andykarpov/karabas-megabuzz/docs/karabas-megabuzz_revA1_bottom.png

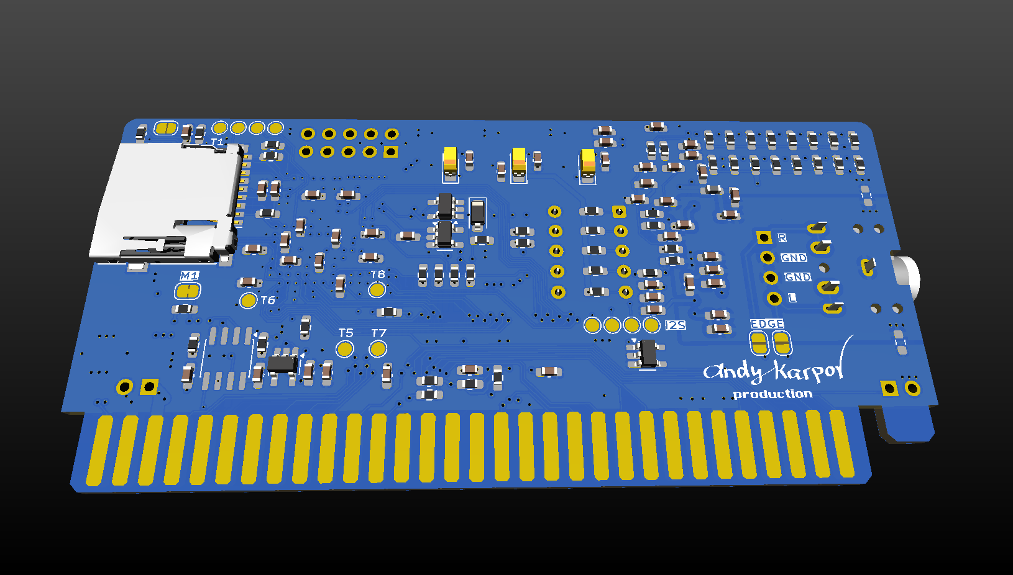
docs/karabas-megabuzz_revA1_bottom.png
