andykarpov/karabas-megabuzz/docs/karabas-megabuzz_revA2_top_map.png

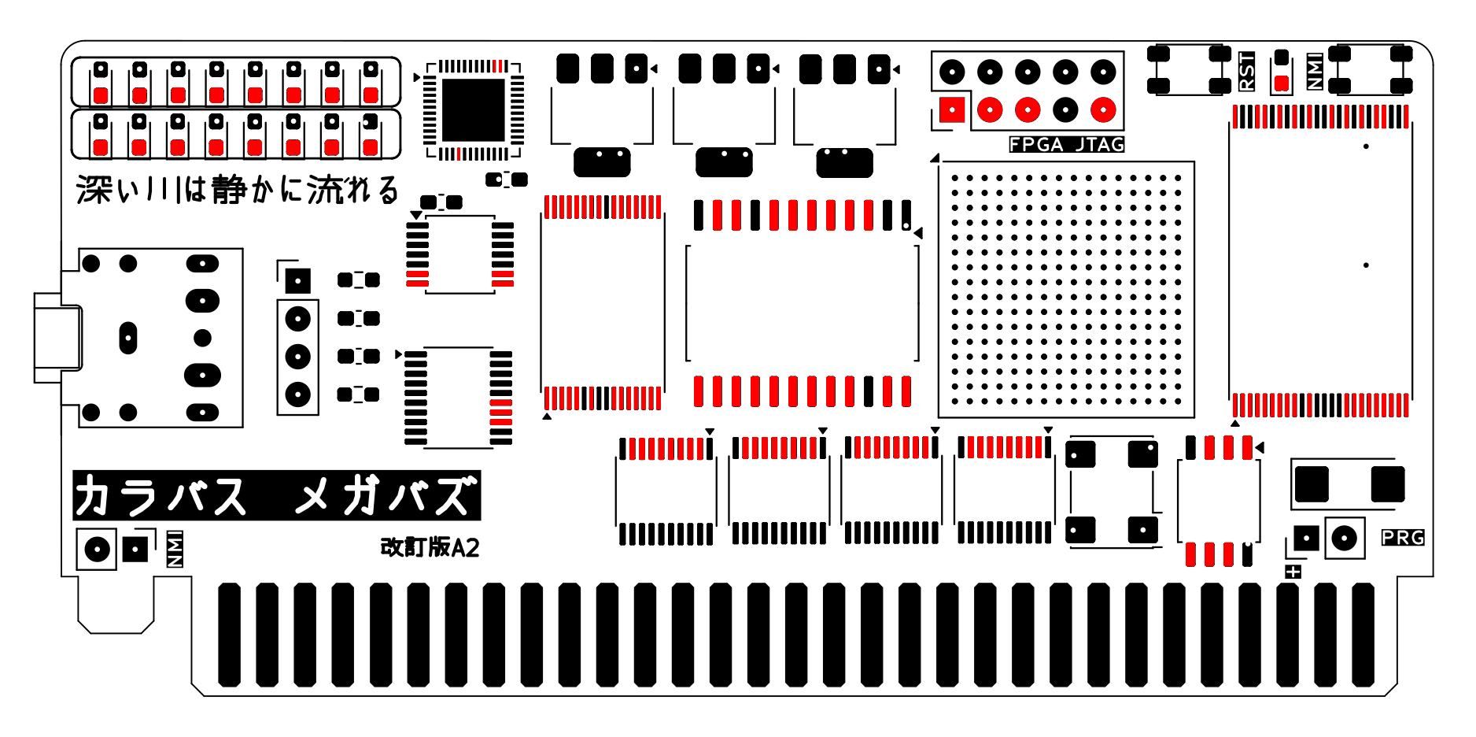
docs/karabas-megabuzz_revA2_top_map.png
