andykarpov/karabas-megabuzz/docs/karabas-megabuzz_revA_top_map.png

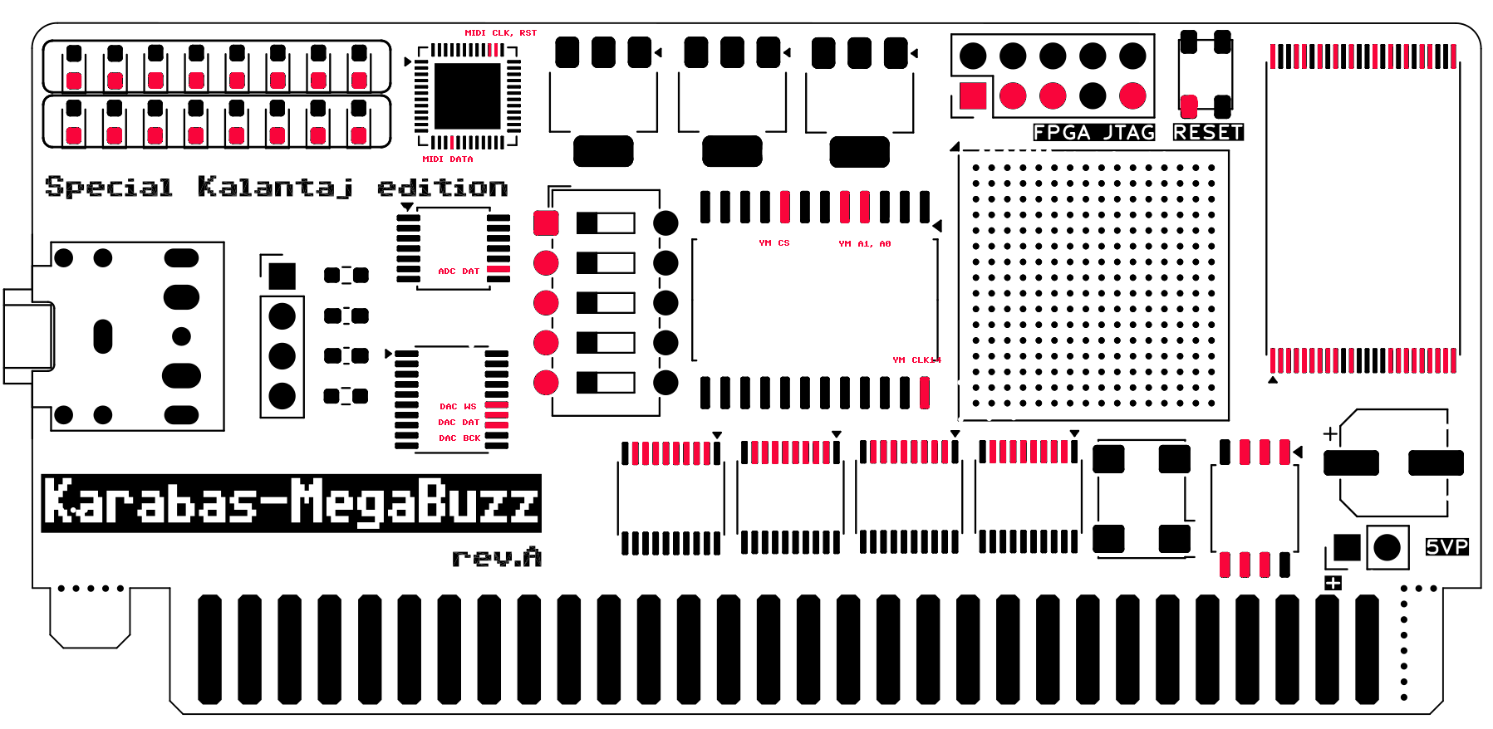
docs/karabas-megabuzz_revA_top_map.png
