andykarpov/karabas-megabuzz/firmware/src/rtl/top_a2.v

/*-------------------------------------------------------------------------------------------------------------------
-- 
-- 
-- #       #######                                                 #                                               
-- #                                                               #                                               
-- #                                                               #                                               
-- ############### ############### ############### ############### ############### ############### ############### 
-- #             #               # #                             # #             #               # #               
-- #             # ############### #               ############### #             # ############### ############### 
-- #             # #             # #               #             # #             # #             #               # 
-- #             # ############### #               ############### ############### ############### ############### 
--                                                                                                                 
--         ####### ####### ####### #######          ## ##   ######  #####   #####  ######  #     # ####### #######
--                                                 #  #  # #       #       #     # #     # #     #      ##      ##
--                                                 #  #  # #####   #   ### ####### ######  #     #   ###     ### 
--                                                 #  #  # #       #     # #     # #     # #     # ##      ##     
--                                                 #  #  #  ######  #####  #     # ######   #####  ####### #######
--
-- https://github.com/andykarpov/karabas-megabuzz
-- FPGA firmware for Karabas-MegaBuzz soundcard revA2
--
-- @author Andy Karpov <andy.karpov@gmail.com>
-- EU, 2026
------------------------------------------------------------------------------------------------------------------*/
`default_nettype none

module karabas_megabuzz_a2(
    input wire          clk,
    input wire  [5:5]   cfg_n,
    input wire          btn_reset_n,
    input wire          btn_nmi_n,

    output wire         o_reset_n,
    input wire          bus_rst_n,
    input wire  [15:0]  bus_a,
    inout wire  [7:0]   bus_d,
    input wire          bus_rd_n,
    input wire          bus_wr_n,
    input wire          bus_iorq_n,
    input wire          bus_mreq_n,
    input wire          bus_m1_n,
    output wire         bus_wait_n,
    output wire         bus_iorqge_n,
    inout wire          bus_nmi_n,
    output wire         bus_romcs_n,
    input wire          bus_f14,

    output wire         midi_clk,
    output wire         midi_tx,
    output wire         midi_reset_n,

    output wire [20:0]  mem_a,
    inout wire  [7:0]   mem_d,
    output wire         mem_wr_n,
    output wire         mem_rd_n,

    output wire [16:13] mmc_mem_a,
    output wire         mmc_mem_cs_n,
    output wire         mmc_mem_rd_n,
    output wire         mmc_mem_wr_n,

    inout wire          sda,
    inout wire          scl,

    output wire         opl3_clk,
    output wire [1:0]   opl3_a,
    output wire         opl3_cs_n,
    input wire  [1:0]   opl3_smp,
    input wire          opl3_data,
    input wire          opl3_dclk,

    output wire         adc_clk,
    output wire         adc_bck,
    output wire         adc_lrck,
    input wire          adc_dat,

    output wire         dac_bck,
    output wire         dac_ws,
    output wire         dac_dat,

    output wire         flash_cs_n,
    output wire         flash_sck,
    inout wire          flash_mosi,
    inout wire          flash_miso,
    inout wire          flash_hold_n,
    inout wire          flash_wp_n,
    output wire         psram_cs_n,

    output wire         sd_cs_n,
    output wire         sd_clk,
    inout wire          sd_di,
    inout wire          sd_do,
    input wire          sd_det_n,

    output wire [7:0]   led_meter_l,
    output wire [7:0]   led_meter_r,

    output wire         led1,

    inout wire  [4:1]   tp
);

// unused signals
assign flash_hold_n = 1'b1;
assign flash_wp_n   = 1'b1;
assign psram_cs_n   = 1'b1;
assign tp[4:1]      = 4'bz;
assign led1         = sd_cs_n;
assign sda          = 1'bz;
assign scl          = 1'b1;

// config bits expanded to named signals
wire [7:0] cfg_byte; // todo: fetch cfg from flash (default) + eeprom
wire divmmc_en      = cfg_byte[0];
wire zc_en          = cfg_byte[1];
wire soundrive_en   = cfg_byte[2];
wire beeper_en      = cfg_byte[3];
wire saa_en         = cfg_byte[4];
wire gs_en          = cfg_byte[5];
wire turbosound_en  = cfg_byte[6];
wire midi_en        = cfg_byte[6]; // depends on AY port
wire opl3_en        = cfg_byte[7];

wire vu_reverse     = ~cfg_n[5]; // solder jumper (reversed VU meters)

// pll
wire clk_bus, clk_mem, clk12, locked, areset;
pll pll_inst(
    .CLK_IN1         (clk),
    .CLK_OUT1        (clk_mem), // 140
    .CLK_OUT2        (clk_bus), // 28
    .CLK_OUT3        (clk12),   // 12
    .LOCKED          (locked)
);
assign areset = ~locked;

// poweron reset
wire poweron_reset;
resetter poweron_resetter(.clk(clk_bus), .areset(divmmc_en & loader_reset), .reset_in(divmmc_en & loader_reset), .reset_out(poweron_reset));

assign o_reset_n = (poweron_reset) ? 1'b0 : 1'bz;

// clock for gs and opl3
reg ce_14m;
always @(negedge clk_bus)
    ce_14m <= !ce_14m;

// reset
wire reset;
wire reset_short;
resetter resetter(.clk(clk_bus), .areset(areset), .reset_in(~bus_rst_n || ~btn_reset_n || poweron_reset), .reset_out(reset), .reset_short(reset_short));

assign midi_reset_n = ~reset;

// bus_iorq_n is useless on zxevo :(
// so we're detecting bus_iorq_n cycle by bus_rd_n/bus_wr_n signal asserted without bus_m1_n/bus_mreq_n
reg ioreq, ioreq_prev;
always @(negedge clk_mem) begin
    ioreq_prev  <= ioreq;
    ioreq       <= bus_m1_n && bus_mreq_n && (~bus_rd_n || ~bus_wr_n);
end
wire ioreq_rd = ioreq && ~bus_rd_n;
wire ioreq_wr = ioreq && ~bus_wr_n;

// bus_dos_n is useless on zxevo :(
// so we're just lock some ports access when instruction has been fetched from rom
reg rom_m1_access;
always @(negedge clk_mem or posedge reset) begin
    if (reset)
        rom_m1_access <= 0;
    else if (~bus_m1_n)
        rom_m1_access <= bus_a[15:14] == 2'b00;
end

// ------- flash ----------------
wire [23:0] flash_a_bus;
wire [7:0] flash_do_bus;
wire flash_wr_n, flash_rd_n, flash_er_n, flash_busy, flash_rdy;
flash flash(
    .CLK              (clk_bus),
    .RESET            (areset),

    .A                (flash_a_bus),
    .DI               (8'hFF),
    .DO               (flash_do_bus),
    .WR_N             (1'b1),
    .RD_N             (flash_rd_n),
    .ER_N             (1'b1),
    
    .DATA0            (flash_miso),
    .NCSO             (flash_cs_n),
    .DCLK             (flash_sck),
    .ASDO             (flash_mosi),

    .BUSY             (flash_busy),
    .DATA_READY       (flash_rdy)
);

// -------- loader --------------
wire [20:0] loader_ram_a;
wire [7:0] loader_ram_do;
wire loader_act, loader_reset, loader_ram_wr;
loader loader(
    .CLK              (clk_bus),
    .RESET            (areset),
    
    .RAM_A            (loader_ram_a),
    .RAM_DO           (loader_ram_do),
    .RAM_WR           (loader_ram_wr),

    .CFG              (cfg_byte),

    .FLASH_A          (flash_a_bus),
    .FLASH_DO         (flash_do_bus),
    .FLASH_RD_N       (flash_rd_n),
    .FLASH_BUSY       (flash_busy),
    .FLASH_READY      (flash_rdy),
    
    .LOADER_ACTIVE    (loader_act),
    .LOADER_RESET     (loader_reset)
);

// ------- i2s DAC --------------
wire signed [15:0] audio_mix_l, audio_mix_r;

PCM5102 #(.DAC_CLK_DIV_BITS(2)) dac_inst(
    .clk              (clk_bus),
    .reset            (reset),
    .left             (audio_mix_l),
    .right            (audio_mix_r),
    .din              (dac_dat),
    .bck              (dac_bck),
    .lrck             (dac_ws)
);

// ------- PCM1808 ADC ---------
wire signed [23:0] adc_l, adc_r;

i2s_transceiver adc_inst(
    .reset_n          (~reset),
    .mclk             (clk_bus),
    .sclk             (adc_bck),
    .ws               (adc_lrck),
    .sd_tx            (),
    .sd_rx            (adc_dat),
    .l_data_tx        (24'b0),
    .r_data_tx        (24'b0),
    .l_data_rx        (adc_l),
    .r_data_rx        (adc_r)
);

ODDR2 oddr_adc2(.Q(adc_clk), .C0(clk_bus), .C1(~clk_bus), .CE(1'b1), .D0(1'b1), .D1(1'b0), .R(1'b0), .S(1'b0));
ODDR2 oddr_midi(.Q(midi_clk), .C0(clk12), .C1(~clk12), .CE(1'b1), .D0(1'b1), .D1(1'b0), .R(1'b0), .S(1'b0));

// ------- SOUNDRIVE ----------
wire [7:0] covox_a, covox_b, covox_c, covox_d, covox_fb;

soundrive soundrive_inst(
    .clk              (clk_bus),
    .reset            (reset),
    .cs               (soundrive_en),
    .a                (bus_a),
    .d                (bus_d),
    .ioreq_wr         (ioreq_wr),
    .rom_m1_access    (rom_m1_access),
    .out_a            (covox_a),
    .out_b            (covox_b),
    .out_c            (covox_c),
    .out_d            (covox_d),
    .out_fb           (covox_fb)
);

// ------- BEEPER --------------
wire beeper;
beeper beeper_inst(
    .clk              (clk_bus),
    .reset            (reset),
    .cs               (beeper_en),
    .a                (bus_a),
    .d                (bus_d),
    .ioreq_wr         (ioreq_wr),
    .out_beeper       (beeper)
);

// SAA1099

wire [7:0] saa_out_l, saa_out_r;
wire saa_wr_n = ~(ioreq_wr && bus_a[7:0] == 8'hFF && ~rom_m1_access);

wire ce_8;
clk_div_8mhz saa1099_cen_inst(
    .clk              (clk_bus),
    .rst_n            (~areset),
    .cen              (ce_8)
);

saa1099 saa1099_inst(
    .clk_sys          (clk_bus),
     .ce              (ce_8),
    .rst_n            (~reset),
    .cs_n             (~saa_en),
    .a0               (bus_a[8]),
    .wr_n             (saa_wr_n),
    .din              (bus_d),
    .out_l            (saa_out_l),
    .out_r            (saa_out_r)
);

// turbosound fm
wire ts_enable = turbosound_en & ioreq & bus_a[15] & (bus_a[3:0] == 4'b1101);
wire ts_we     = ts_enable & ioreq_wr;
wire [7:0] ts_do;
wire [7:0] ts_ssg0_a, ts_ssg0_b, ts_ssg0_c, ts_ssg1_a, ts_ssg1_b, ts_ssg1_c;
wire [15:0] ts_ssg0_fm, ts_ssg1_fm;
wire ts_fm_ena;

reg ce_ym;
reg [2:0] div;
always @(posedge clk_bus) begin
    div <= div + 1'd1;
    ce_ym <= !div[2] & !div[1] & !div[0]; // 3.5
end

turbosound turbosound_inst(
    .CLK              (clk_bus),
    .RESET            (reset),
    .CE               (ce_ym),
    .BDIR             (ts_we),
    .BC               (bus_a[14]),
    .DI               (bus_d),
    .DO               (ts_do),
    .AY_MODE          (1'b0), // ay / ym
        
    .SSG0_AUDIO_A     (ts_ssg0_a),
    .SSG0_AUDIO_B     (ts_ssg0_b),
    .SSG0_AUDIO_C     (ts_ssg0_c),

    .SSG1_AUDIO_A     (ts_ssg1_a),
    .SSG1_AUDIO_B     (ts_ssg1_b),
    .SSG1_AUDIO_C     (ts_ssg1_c),
    
    .SSG0_AUDIO_FM    (ts_ssg0_fm),
    .SSG1_AUDIO_FM    (ts_ssg1_fm),
    
    .SSG_FM_ENA       (ts_fm_ena),
    .MIDI_TX          (midi_tx)
);

// ------- GS

wire gs_oe;
wire [7:0] gs_do_bus;
wire [14:0] gs_out_l, gs_out_r;

gs_top gs_inst(
    .clk_bus          (clk_bus),
     .ce              (ce_14m),
    .reset            (reset),

    .a                (bus_a),
    .di               (bus_d),
    .mreq_n           (bus_mreq_n),
    .iorq_n           (bus_iorq_n),
    .m1_n             (bus_m1_n),
    .rd_n             (bus_rd_n),
    .wr_n             (bus_wr_n),

    .oe               (gs_oe),
    .do_bus           (gs_do_bus),

    .sram_d           (mem_d),
    .sram_a           (mem_a),
    .sram_wr_n        (mem_wr_n),
    .sram_rd_n        (mem_rd_n),
     
    .loader_act       (loader_act),
    .loader_ram_a     (loader_ram_a),
    .loader_ram_do    (loader_ram_do),
    .loader_ram_wr    (loader_ram_wr),

    .out_l            (gs_out_l),
    .out_r            (gs_out_r)    
);

// opl3

wire signed [15:0] opl3_l, opl3_r;
opl3 opl3_inst(
    .clk              (clk_bus),
    .ce               (ce_14m),
    .en               (opl3_en),
    .reset            (reset),
    
    .bus_a            (bus_a),
    .bus_d            (bus_d),
    .bus_rd_n         (bus_rd_n),
    .bus_wr_n         (bus_wr_n),
    .bus_mreq_n       (bus_mreq_n),
    .bus_iorq_n       (bus_iorq_n),
    .bus_m1_n         (bus_m1_n),    
    
    .opl3_clk         (opl3_clk),
    .opl3_a           (opl3_a),
    .opl3_cs_n        (opl3_cs_n),

    .opl3_smp         (opl3_smp),
    .opl3_data        (opl3_data),
    .opl3_dclk        (opl3_dclk),
    
    .out_l            (opl3_l),
    .out_r            (opl3_r)
);

// midi activity detector
wire midi_active;
midi_tx_sensor midi_tx_sensor(
    .clk              (clk_bus),
    .reset            (reset),
    .midi_in          (midi_tx),
    .midi_active      (midi_active)
);

// audio muter on reset
wire mute;
audio_mute audio_mute(
    .clk              (clk_bus),
    .on               (reset),
    .mute             (mute)
);

// audio mixer
audio_mixer audio_mixer_inst(
    .clk              (clk_bus),

    .mute             (mute), 
    .mode             (2'b00), // abc/acb/mono ? 
    
    .soundrive_en     (soundrive_en),
    .beeper_en        (beeper_en),
    .turbosound_en    (turbosound_en),
    .saa_en           (saa_en),
    .gs_en            (gs_en),
    .midi_en          (midi_en & midi_active),
    .opl3_en          (opl3_en),
    
    .speaker          (beeper),
    .tape_in          (1'b0),
    
    .ssg0_a           (ts_ssg0_a),
    .ssg0_b           (ts_ssg0_b),
    .ssg0_c           (ts_ssg0_c),
    .ssg1_a           (ts_ssg1_a),
    .ssg1_b           (ts_ssg1_b),
    .ssg1_c           (ts_ssg1_c),
    
    .covox_a          (covox_a),
    .covox_b          (covox_b),
    .covox_c          (covox_c),
    .covox_d          (covox_d),
    .covox_fb         (covox_fb),
    
    .saa_l            (saa_out_l),
    .saa_r            (saa_out_r),
    
    .gs_l             (gs_out_l),
    .gs_r             (gs_out_r),
    
    .fm_l             (ts_ssg0_fm),
    .fm_r             (ts_ssg1_fm),
    .fm_ena           (ts_fm_ena),

    .adc_l            (adc_l[23:8]),
    .adc_r            (adc_r[23:8]),
    
    .opl3_l           (opl3_l),
    .opl3_r           (opl3_r),
    
    .audio_l          (audio_mix_l),
    .audio_r          (audio_mix_r)    
);

// divmmc + zc
wire [7:0] zc_do_bus, divmmc_dout;
wire zc_busy, divmmc_mem, divmmc_zxrom_block;
zc_divmmc zc_divmmc(
    .clk              (clk_bus),
    .clk_mem          (clk_mem),
    .reset            (reset_short),
    .areset           (areset | poweron_reset),
    .divmmc_en        (divmmc_en),
    .zc_en            (zc_en),

    .bus_a            (bus_a),
    .bus_d            (bus_d),
    .bus_iorq_n       (bus_iorq_n),
    .bus_mreq_n       (bus_mreq_n),
    .bus_m1_n         (bus_m1_n),
    .bus_wr_n         (bus_wr_n),
    .bus_rd_n         (bus_rd_n),
    .bus_nmi_n        (bus_nmi_n),
    .btn_nmi_n        (btn_nmi_n),

    .ram_a            (mmc_mem_a),
    .ram_cs_n         (mmc_mem_cs_n),
    .ram_rd_n         (mmc_mem_rd_n),
    .ram_wr_n         (mmc_mem_wr_n),

    .sd_clk           (sd_clk),
    .sd_do            (sd_do),
    .sd_di            (sd_di),
    .sd_cs_n          (sd_cs_n),
    
    .dout             (zc_do_bus),
    .divmmc_mem       (divmmc_mem),
    .divmmc_dout      (divmmc_dout),
    .divmmc_zxrom_block(divmmc_zxrom_block),
    .busy             (zc_busy)
);

// IORQGE

// turbosound ports
wire port_bffd      = (bus_a[15:14] == 2'b10) & (bus_a[3:0] == 4'b1101) & turbosound_en;
wire port_fffd      = (bus_a[15:14] == 2'b11) & (bus_a[3:0] == 4'b1101) & turbosound_en;
wire port_fffd_full = (bus_a[15:13] == 3'b111) & (bus_a[3:0] == 4'b1101) & turbosound_en; // required for compatibility with #dffd port
// gs (b3,bb)
wire port_gs = ((bus_a[7:0] == 8'hB3) | (bus_a[7:0] == 8'hBB)) & gs_en & ~loader_act;
// opl3 (c4,c5,c6,c7)
wire port_opl3 = (bus_a[7:2] == 6'b110001) & opl3_en;
// zc + divmmc
wire port_zc = (((bus_a[7:0] == 8'h77) & (zc_en | divmmc_en)) | 
                ((bus_a[7:0] == 8'h57) & (zc_en | divmmc_en)) | 
                ((bus_a[7:0] == 8'hEB) & divmmc_en));
wire port_mmc = ((bus_a[7:0] == 8'hE3) | (bus_a[7:0] == 8'hE7)) & divmmc_en;

// iorqge
assign bus_iorqge_n = (port_fffd_full | port_bffd | port_gs | port_opl3 | port_zc | port_mmc) ? 1'b0 : 1'b1;

// BUS
assign bus_d = 
     (divmmc_en & divmmc_mem & ~bus_mreq_n & ~bus_rd_n) ? divmmc_dout : // DivMMC memory dout
     (~bus_iorq_n & ~bus_rd_n & bus_m1_n & port_zc) ? zc_do_bus : // ZC + DivMMC
     (ioreq_rd & port_fffd) ? ts_do : // TS
     (~bus_iorq_n & ~bus_rd_n & bus_m1_n & port_gs) ? gs_do_bus : // GS
     8'bzzzzzzzz;
     
// wait (from zc)
assign bus_wait_n = (zc_busy & (divmmc_en | zc_en)) ? 1'b0 : 1'bz;

// block zx rom
assign bus_romcs_n = divmmc_en & divmmc_zxrom_block & ~bus_mreq_n ? 1'b0 : 1'b1;

// vu meter
vu_meter vu_meter_l_inst(
    .clk              (clk_bus),
    .dir              (vu_reverse),
    .enable_bar       (1'b1), // todo: перенести в конфиг?
    .enable_dot       (1'b0), // todo: перенести в конфиг?
    .reset            (reset),
    .sample_tick      (dac_ws),
    .audio_sample     (audio_mix_l),
    .leds             (led_meter_l)
);

vu_meter vu_meter_r_inst(
    .clk              (clk_bus),
    .dir              (vu_reverse),
    .enable_bar       (1'b1), // todo: перенести в конфиг?
    .enable_dot       (1'b0), // todo: перенести в конфиг?
    .reset            (reset),
    .sample_tick      (dac_ws),
    .audio_sample     (audio_mix_r),
    .leds             (led_meter_r)
);

endmodule
