andykarpov/karabas-megabuzz/firmware/src/rtl/pll/pll.v

// file: pll.v
// 
// (c) Copyright 2008 - 2011 Xilinx, Inc. All rights reserved.
// 
// This file contains confidential and proprietary information
// of Xilinx, Inc. and is protected under U.S. and
// international copyright and other intellectual property
// laws.
// 
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
// CRITICAL APPLICATIONS
// Xilinx products are not designed or intended to be fail-
// safe, or for use in any application requiring fail-safe
// performance, such as life-support or safety devices or
// systems, Class III medical devices, nuclear facilities,
// applications related to the deployment of airbags, or any
// other applications that could lead to death, personal
// injury, or severe property or environmental damage
// (individually and collectively, "Critical
// Applications"). Customer assumes the sole risk and
// liability of any use of Xilinx products in Critical
// Applications, subject only to applicable laws and
// regulations governing limitations on product liability.
// 
// THIS COPYRIGHT NOTICE AND DISCLAIMER MUST BE RETAINED AS
// PART OF THIS FILE AT ALL TIMES.
// 
//----------------------------------------------------------------------------
// User entered comments
//----------------------------------------------------------------------------
// None
//
//----------------------------------------------------------------------------
// "Output    Output      Phase     Duty      Pk-to-Pk        Phase"
// "Clock    Freq (MHz) (degrees) Cycle (%) Jitter (ps)  Error (ps)"
//----------------------------------------------------------------------------
// CLK_OUT1___140.000______0.000______50.0______210.491____199.399
// CLK_OUT2____28.000______0.000______50.0______297.991____199.399
// CLK_OUT3____12.069______0.000______50.0______352.195____199.399
//
//----------------------------------------------------------------------------
// "Input Clock   Freq (MHz)    Input Jitter (UI)"
//----------------------------------------------------------------------------
// __primary__________50.000____________0.010

`timescale 1ps/1ps

(* CORE_GENERATION_INFO = "pll,clk_wiz_v3_6,{component_name=pll,use_phase_alignment=true,use_min_o_jitter=false,use_max_i_jitter=false,use_dyn_phase_shift=false,use_inclk_switchover=false,use_dyn_reconfig=false,feedback_source=FDBK_AUTO,primtype_sel=PLL_BASE,num_out_clk=3,clkin1_period=20.000,clkin2_period=20.000,use_power_down=false,use_reset=false,use_locked=true,use_inclk_stopped=false,use_status=false,use_freeze=false,use_clk_valid=false,feedback_type=SINGLE,clock_mgr_type=AUTO,manual_override=false}" *)
module pll
 ( // Clock in ports
  input wire        CLK_IN1,
  // Clock out ports
  output wire       CLK_OUT1,
  output wire       CLK_OUT2,
  output wire       CLK_OUT3,
  // Status and control signals
  output wire       LOCKED
);

  // Input buffering
  //------------------------------------
  wire clkin1;
  IBUFG clkin1_buf
  (.O (clkin1),
    .I (CLK_IN1));


  // Clocking primitive
  //------------------------------------
  // Instantiation of the PLL primitive
  //    * Unused inputs are tied off
  //    * Unused outputs are labeled unused
  wire [15:0] do_unused;
  wire        drdy_unused;
  wire        clkfbout;
  wire        clkfbout_buf;
  wire        clkout0, clkout1, clkout2;
  wire        clkout3_unused;
  wire        clkout4_unused;
  wire        clkout5_unused;

  PLL_BASE
  #(.BANDWIDTH              ("OPTIMIZED"),
    .CLK_FEEDBACK           ("CLKFBOUT"),
    .COMPENSATION           ("SYSTEM_SYNCHRONOUS"),
    .DIVCLK_DIVIDE          (1),
    .CLKFBOUT_MULT          (14),
    .CLKFBOUT_PHASE         (0.000),
    .CLKOUT0_DIVIDE         (5),
    .CLKOUT0_PHASE          (0.000),
    .CLKOUT0_DUTY_CYCLE     (0.500),
    .CLKOUT1_DIVIDE         (25),
    .CLKOUT1_PHASE          (0.000),
    .CLKOUT1_DUTY_CYCLE     (0.500),
    .CLKOUT2_DIVIDE         (58),
    .CLKOUT2_PHASE          (0.000),
    .CLKOUT2_DUTY_CYCLE     (0.500),
    .CLKIN_PERIOD           (20.000),
    .REF_JITTER             (0.010))
  pll_base_inst
  // Output clocks
  (.CLKFBOUT              (clkfbout),
    .CLKOUT0               (clkout0),
    .CLKOUT1               (clkout1),
    .CLKOUT2               (clkout2),
    .CLKOUT3               (clkout3_unused),
    .CLKOUT4               (clkout4_unused),
    .CLKOUT5               (clkout5_unused),
    // Status and control signals
    .LOCKED                (LOCKED),
    .RST                   (1'b0),
    // Input clock control
    .CLKFBIN               (clkfbout_buf),
    .CLKIN                 (clkin1));


  // Output buffering
  //-----------------------------------
  BUFG clkf_buf
  (.O (clkfbout_buf),
    .I (clkfbout));

  BUFG clkout1_buf
  (.O   (CLK_OUT1),
    .I   (clkout0));


  BUFG clkout2_buf
  (.O   (CLK_OUT2),
    .I   (clkout1));

  BUFG clkout3_buf
  (.O   (CLK_OUT3),
    .I   (clkout2));



endmodule
