andykarpov/karabas-megabuzz/firmware/src/rtl/core/neorv32_imem_image.vhd

library ieee;
use ieee.std_logic_1164.all;

package neorv32_imem_image is

type rom_t is array (0 to 16383) of std_ulogic_vector(31 downto 0);
constant image_size_c : natural := 42204;
constant image_data_c : rom_t := (
x"f14020f3",
x"80008217",
x"ffc20213",
x"ff027113",
x"80000197",
x"7f018193",
x"000022b7",
x"80028293",
x"30029073",
x"00000317",
x"15030313",
x"30531073",
x"30401073",
x"0000a397",
x"cd438393",
x"80000417",
x"fc440413",
x"80000497",
x"79048493",
x"80000517",
x"78850513",
x"80002597",
x"a0058593",
x"46814601",
x"47814701",
x"48814801",
x"49814901",
x"4a814a01",
x"4b814b01",
x"4c814c01",
x"4d814d01",
x"4e814e01",
x"4f814f01",
x"04008263",
x"00000797",
x"01c78793",
x"30579073",
x"30445073",
x"30046073",
x"10500073",
x"0001bff5",
x"00000797",
x"0d078793",
x"30579073",
x"30405073",
x"fff44737",
x"00872103",
x"07374750",
x"2223fff4",
x"a8810007",
x"00838b63",
x"00947963",
x"0003a783",
x"0391c01c",
x"6be30411",
x"7763fe94",
x"202300b5",
x"05110005",
x"feb56de3",
x"00006417",
x"54040413",
x"00006497",
x"53848493",
x"00947963",
x"00042083",
x"000080e7",
x"6be30411",
x"0617fe94",
x"06130000",
x"000f0dc6",
x"100f0ff0",
x"45010000",
x"00e74581",
x"70730006",
x"10733004",
x"05973040",
x"85930000",
x"90730465",
x"10733055",
x"24733405",
x"e00df140",
x"00006417",
x"4e840413",
x"00006497",
x"4e048493",
x"00940863",
x"22831471",
x"80e70004",
x"bfcd0002",
x"f1402473",
x"9002e011",
x"10500073",
x"0001bff5",
x"10500073",
x"ffdff06f",
x"11010001",
x"c64ec84a",
x"09b76905",
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
x"00000000",
x"00000000",
x"00000000",
x"00000000",
x"00000000",
x"00000000",
x"00000000",
x"00000000",
x"00000000",
x"00000000",
x"00000000",
x"00000000",
x"00000000",
x"00000000",
x"00000000",
x"00000000",
x"00000000",
x"00000000",
x"00000000",
x"00000000",
x"00000000",
x"00000000",
x"00000000",
x"00000000",
x"00000000",
x"00000000",
x"00000000",
x"00000000",
x"00000000",
x"00000000",
x"00000000",
x"00000001",
x"00000000",
x"abcd330e",
x"e66d1234",
x"0005deec",
x"0000000b",
x"00000000",
x"00000000",
x"00000000",
x"00000000",
x"00000000",
x"00000000",
x"00000000",
x"00000000",
x"00000000",
x"00000000",
x"00000000",
x"00000000",
x"00000000",
x"00000000",
x"00000000",
x"00000000",
x"00000000",
x"00000000",
x"00000000",
x"00000000",
x"00000000",
x"00000000",
x"00000000",
x"00000000",
x"00000000",
x"00000000",
x"00000000",
x"00000000",
x"00000000",
x"00000000",
x"00000000",
x"00000000",
x"00000000",
x"00000000",
x"00000000",
x"00000000",
x"ffffffff",
x"00020000",
x"80000688",
others => (others => '0')
);

end package;
