andykarpov/karabas-megabuzz/firmware/src/rtl/adc/i2s_transceiver.vhd

--------------------------------------------------------------------------------
--
--   FileName:         i2s_transceiver.vhd
--   Dependencies:     none
--   Design Software:  Quartus Prime Version 17.0.0 Build 595 SJ Lite Edition
--
--   HDL CODE IS PROVIDED "AS IS."  DIGI-KEY EXPRESSLY DISCLAIMS ANY
--   WARRANTY OF ANY KIND, WHETHER EXPRESS OR IMPLIED, INCLUDING BUT NOT
--   LIMITED TO, THE IMPLIED WARRANTIES OF MERCHANTABILITY, FITNESS FOR A
--   PARTICULAR PURPOSE, OR NON-INFRINGEMENT. IN NO EVENT SHALL DIGI-KEY
--   BE LIABLE FOR ANY INCIDENTAL, SPECIAL, INDIRECT OR CONSEQUENTIAL
--   DAMAGES, LOST PROFITS OR LOST DATA, HARM TO YOUR EQUIPMENT, COST OF
--   PROCUREMENT OF SUBSTITUTE GOODS, TECHNOLOGY OR SERVICES, ANY CLAIMS
--   BY THIRD PARTIES (INCLUDING BUT NOT LIMITED TO ANY DEFENSE THEREOF),
--   ANY CLAIMS FOR INDEMNITY OR CONTRIBUTION, OR OTHER SIMILAR COSTS.
--
--   Version History
--   Version 1.0 03/29/2019 Scott Larson
--     Initial Public Release
-- 
--------------------------------------------------------------------------------

LIBRARY ieee;
USE ieee.std_logic_1164.all;

ENTITY i2s_transceiver IS
  GENERIC(
    mclk_sclk_ratio : INTEGER := 8;     --number of mclk periods per sclk period
    sclk_ws_ratio   : INTEGER := 64;    --number of sclk periods per word select period
    d_width         : INTEGER := 24);   --data width
  PORT(
    reset_n   : IN  STD_LOGIC;          --asynchronous active low reset
    mclk      : IN  STD_LOGIC;          --master clock
    sclk      : OUT STD_LOGIC;          --serial clock (or bit clock)
    ws        : OUT STD_LOGIC;          --word select (or left-right clock)
    sd_tx     : OUT STD_LOGIC;          --serial data transmit
    sd_rx     : IN  STD_LOGIC;          --serial data receive
    l_data_tx : IN  STD_LOGIC_VECTOR(d_width - 1 DOWNTO 0); --left channel data to transmit
    r_data_tx : IN  STD_LOGIC_VECTOR(d_width - 1 DOWNTO 0); --right channel data to transmit
    l_data_rx : OUT STD_LOGIC_VECTOR(d_width - 1 DOWNTO 0); --left channel data received
    r_data_rx : OUT STD_LOGIC_VECTOR(d_width - 1 DOWNTO 0)); --right channel data received
END i2s_transceiver;

ARCHITECTURE logic OF i2s_transceiver IS

  SIGNAL sclk_int      : STD_LOGIC := '0'; --internal serial clock signal
  SIGNAL ws_int        : STD_LOGIC := '0'; --internal word select signal
  SIGNAL l_data_rx_int : STD_LOGIC_VECTOR(d_width - 1 DOWNTO 0); --internal left channel rx data buffer
  SIGNAL r_data_rx_int : STD_LOGIC_VECTOR(d_width - 1 DOWNTO 0); --internal right channel rx data buffer
  SIGNAL l_data_tx_int : STD_LOGIC_VECTOR(d_width - 1 DOWNTO 0); --internal left channel tx data buffer
  SIGNAL r_data_tx_int : STD_LOGIC_VECTOR(d_width - 1 DOWNTO 0); --internal right channel tx data buffer

BEGIN

  PROCESS(mclk, reset_n)
    VARIABLE sclk_cnt : INTEGER := 0;   --counter of master clocks during half period of serial clock
    VARIABLE ws_cnt   : INTEGER := 0;   --counter of serial clock toggles during half period of word select
  BEGIN
    IF (reset_n = '0') THEN             --asynchronous reset
      sclk_cnt      := 0;               --clear mclk/sclk counter
      ws_cnt        := 0;               --clear sclk/ws counter
      sclk_int      <= '0';             --clear serial clock signal
      ws_int        <= '0';             --clear word select signal
      l_data_rx_int <= (OTHERS => '0'); --clear internal left channel rx data buffer
      r_data_rx_int <= (OTHERS => '0'); --clear internal right channel rx data buffer
      l_data_tx_int <= (OTHERS => '0'); --clear internal left channel tx data buffer
      r_data_tx_int <= (OTHERS => '0'); --clear internal right channel tx data buffer
      sd_tx         <= '0';             --clear serial data transmit output
      l_data_rx     <= (OTHERS => '0'); --clear left channel received data output
      r_data_rx     <= (OTHERS => '0'); --clear right channel received data output
    ELSIF (mclk'EVENT AND mclk = '1') THEN --master clock rising edge
      IF (sclk_cnt < mclk_sclk_ratio / 2 - 1) THEN --less than half period of sclk
        sclk_cnt := sclk_cnt + 1;       --increment mclk/sclk counter
      ELSE                              --half period of sclk
        sclk_cnt := 0;                  --reset mclk/sclk counter
        sclk_int <= NOT sclk_int;       --toggle serial clock
        IF (ws_cnt < sclk_ws_ratio - 1) THEN --less than half period of ws
          ws_cnt := ws_cnt + 1;         --increment sclk/ws counter
          IF (sclk_int = '0' AND ws_cnt > 1 AND ws_cnt < d_width * 2 + 2) THEN --rising edge of sclk during data word
            IF (ws_int = '1') THEN      --right channel
              r_data_rx_int <= r_data_rx_int(d_width - 2 DOWNTO 0) & sd_rx; --shift data bit into right channel rx data buffer
            ELSE                        --left channel
              l_data_rx_int <= l_data_rx_int(d_width - 2 DOWNTO 0) & sd_rx; --shift data bit into left channel rx data buffer
            END IF;
          END IF;
          IF (sclk_int = '1' AND ws_cnt < d_width * 2 + 3) THEN --falling edge of sclk during data word
            IF (ws_int = '1') THEN      --right channel
              sd_tx         <= r_data_tx_int(d_width - 1); --transmit serial data bit 
              r_data_tx_int <= r_data_tx_int(d_width - 2 DOWNTO 0) & '0'; --shift data of right channel tx data buffer
            ELSE                        --left channel
              sd_tx         <= l_data_tx_int(d_width - 1); --transmit serial data bit
              l_data_tx_int <= l_data_tx_int(d_width - 2 DOWNTO 0) & '0'; --shift data of left channel tx data buffer
            END IF;
          END IF;
        ELSE                            --half period of ws
          ws_cnt        := 0;           --reset sclk/ws counter
          ws_int        <= NOT ws_int;  --toggle word select
          r_data_rx     <= r_data_rx_int; --output right channel received data
          l_data_rx     <= l_data_rx_int; --output left channel received data
          r_data_tx_int <= r_data_tx;   --latch in right channel data to transmit
          l_data_tx_int <= l_data_tx;   --latch in left channel data to transmit
        END IF;
      END IF;
    END IF;
  END PROCESS;

  sclk <= sclk_int;                     --output serial clock
  ws   <= ws_int;                       --output word select

END logic;
