andykarpov/karabas-megabuzz/firmware/src/rtl/sound/jt12/jt12_kon.v

/* This file is part of JT12.


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
    Author: Jose Tejada Gomez. Twitter: @topapate
    Version: 1.0
    Date: 27-1-2017

*/

module jt12_kon(
    input wire          rst,
    input wire          clk,
    input wire          clk_en /* synthesis direct_enable */,
    input wire  [3:0]   keyon_op,
    input wire  [2:0]   keyon_ch,
    input wire  [1:0]   next_op,
    input wire  [2:0]   next_ch,
    input wire          up_keyon,
    input wire          csm,
    // input            flag_A,
    input wire          overflow_A,

    output  reg     keyon_I
);

parameter num_ch=6;

wire csr_out;

generate
if(num_ch==6) begin
    // capture overflow signal so it lasts long enough
    reg overflow2;
    reg [4:0] overflow_cycle;

    always @(posedge clk) if( clk_en ) begin
        if(overflow_A) begin
            overflow2 <= 1'b1;
            overflow_cycle <= { next_op, next_ch };
        end else begin
            if(overflow_cycle == {next_op, next_ch}) overflow2<=1'b0;
        end
    end

    always @(posedge clk) if( clk_en )
        keyon_I <= (csm&&next_ch==3'd2&&overflow2) || csr_out;

    reg        up_keyon_reg;
    reg  [3:0] tkeyon_op;
    reg  [2:0] tkeyon_ch;
    wire       key_upnow;

    assign key_upnow = up_keyon_reg && (tkeyon_ch==next_ch) && (next_op == 2'd3);

    always @(posedge clk) if( clk_en ) begin
        if (rst)
            up_keyon_reg <= 1'b0;
        if (up_keyon) begin
            up_keyon_reg <= 1'b1;
            tkeyon_op <= keyon_op;
            tkeyon_ch <= keyon_ch;      end
        else if (key_upnow)
            up_keyon_reg <= 1'b0;
     end


    wire middle1;
    wire middle2;
    wire middle3;
    wire din      = key_upnow ? tkeyon_op[3] : csr_out;
    wire mid_din2 = key_upnow ? tkeyon_op[1] : middle1;
    wire mid_din3 = key_upnow ? tkeyon_op[2] : middle2;
    wire mid_din4 = key_upnow ? tkeyon_op[0] : middle3;

    jt12_sh_rst #(.width(1),.stages(6),.rstval(1'b0)) u_konch0(
        .clk    ( clk       ),
        .clk_en ( clk_en    ),
        .rst    ( rst       ),
        .din    ( din       ),
        .drop   ( middle1   )
    );

    jt12_sh_rst #(.width(1),.stages(6),.rstval(1'b0)) u_konch1(
        .clk    ( clk       ),
        .clk_en ( clk_en    ),
        .rst    ( rst       ),
        .din    ( mid_din2  ),
        .drop   ( middle2   )
    );

    jt12_sh_rst #(.width(1),.stages(6),.rstval(1'b0)) u_konch2(
        .clk    ( clk       ),
        .clk_en ( clk_en    ),
        .rst    ( rst       ),
        .din    ( mid_din3  ),
        .drop   ( middle3   )
    );

    jt12_sh_rst #(.width(1),.stages(6),.rstval(1'b0)) u_konch3(
        .clk    ( clk       ),
        .clk_en ( clk_en    ),
        .rst    ( rst       ),
        .din    ( mid_din4  ),
        .drop   ( csr_out   )
    );
end
else begin // 3 channels
    reg din;
    reg [3:0] next_op_hot;

    always @(*) begin
        case( next_op )
            2'd0: next_op_hot = 4'b0001; // S1
            2'd1: next_op_hot = 4'b0100; // S3
            2'd2: next_op_hot = 4'b0010; // S2
            2'd3: next_op_hot = 4'b1000; // S4
            default: ; // no operation
        endcase
        din = keyon_ch[1:0]==next_ch[1:0] && up_keyon ? |(keyon_op&next_op_hot) : csr_out;
    end

    always @(posedge clk) if( clk_en )
        keyon_I <= csr_out; // No CSM for YM2203

    jt12_sh_rst #(.width(1),.stages(12),.rstval(1'b0)) u_konch1(
        .clk    ( clk       ),
        .clk_en ( clk_en    ),
        .rst    ( rst       ),
        .din    ( din       ),
        .drop   ( csr_out   )
    );
end
endgenerate


endmodule
