andykarpov/karabas-megabuzz/firmware/src/rtl/ram/dpram.v

`timescale 1ns / 1ps

module dpram #(parameter DATAWIDTH=8, ADDRWIDTH=8, NUMWORDS=1<<ADDRWIDTH, MEM_INIT_FILE="")
(
	input wire                 clock,

	input wire [ADDRWIDTH-1:0] address_a,
	input wire [DATAWIDTH-1:0] data_a,
	input wire                 wren_a,
	output reg [DATAWIDTH-1:0] q_a,

	input wire [ADDRWIDTH-1:0] address_b,
	input wire [DATAWIDTH-1:0] data_b,
	input wire                 wren_b,
	output reg [DATAWIDTH-1:0] q_b
);

   reg [DATAWIDTH-1:0] mem[0:NUMWORDS];
   initial begin  // usa $readmemb/$readmemh dependiendo del formato del fichero que contenga la ROM
    if (MEM_INIT_FILE != "") begin
      $readmemb(MEM_INIT_FILE, mem);
    end
   end

  always @(posedge clock) 
  begin
    if (wren_a)
    begin
      mem[address_a] <= data_a;
      q_a <= data_a;
    end
    else
      q_a <= mem[address_a];
  end

  always @(posedge clock) 
  begin
    if (wren_b)
    begin
      mem[address_b] <= data_b;
      q_b <= data_b;
    end
    else
      q_b <= mem[address_b];
  end


endmodule
